arpfic/Organous_OSC/Hardware/carte_osc_fonctions_avancees_0.2_top.png

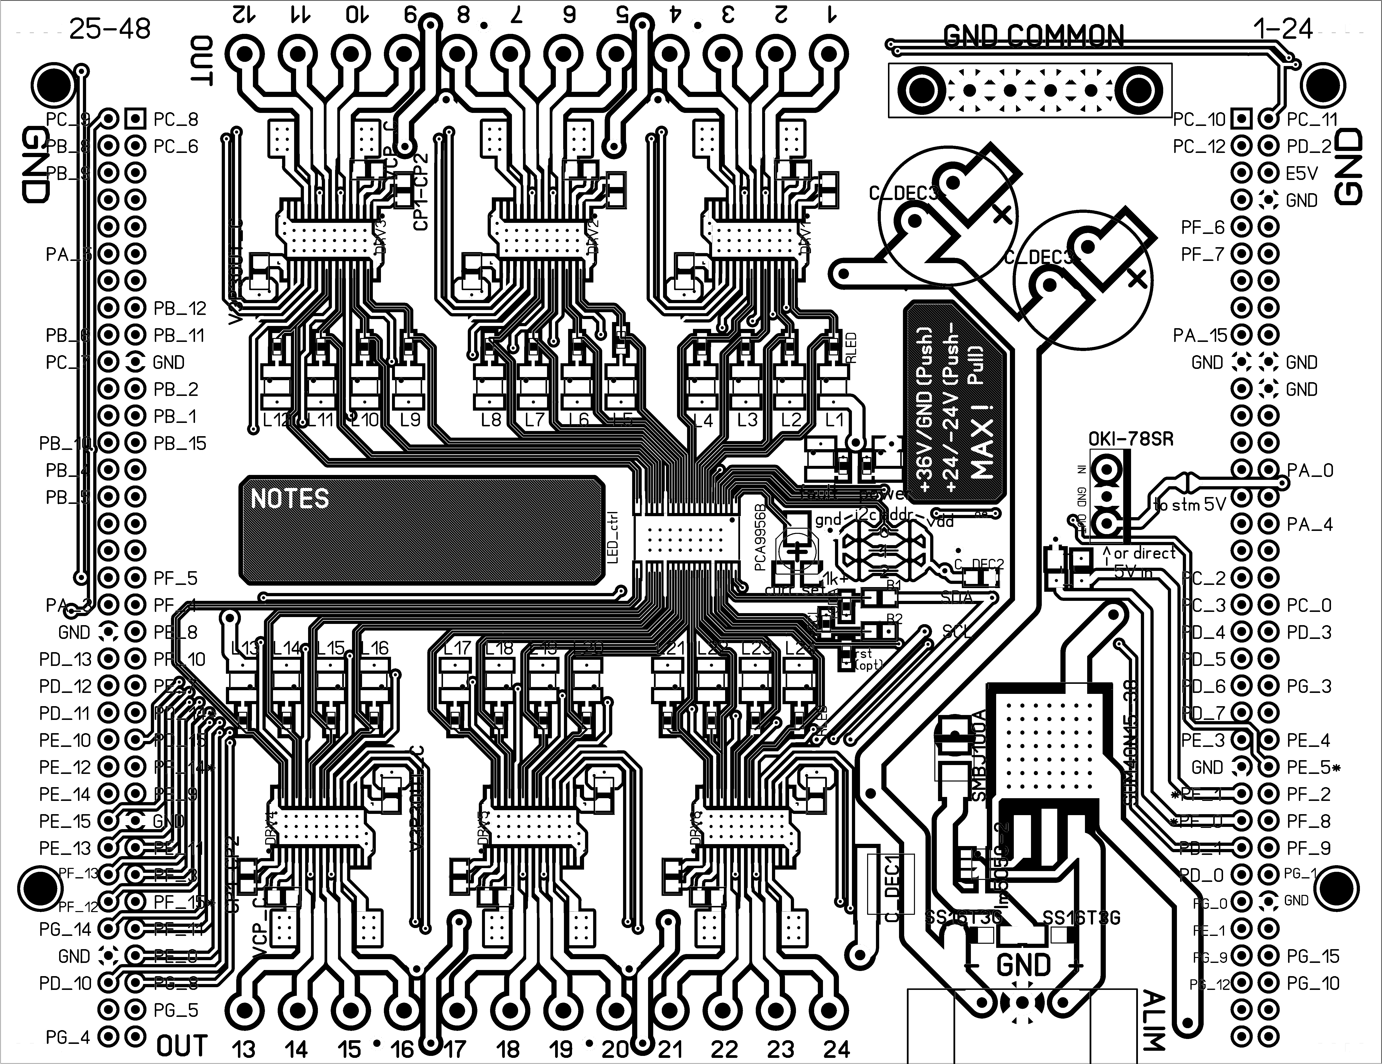
Hardware/carte_osc_fonctions_avancees_0.2_top.png
