arpfic/Organous_OSC/Hardware/carte_osc_schema_fonc.png

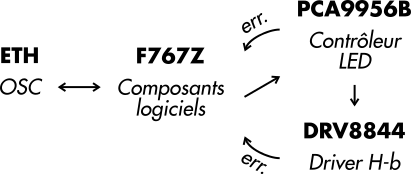
Hardware/carte_osc_schema_fonc.png
