arpfic/Organous_OSC/Hardware/Organous_OSC_v0.2_exemple.jpg

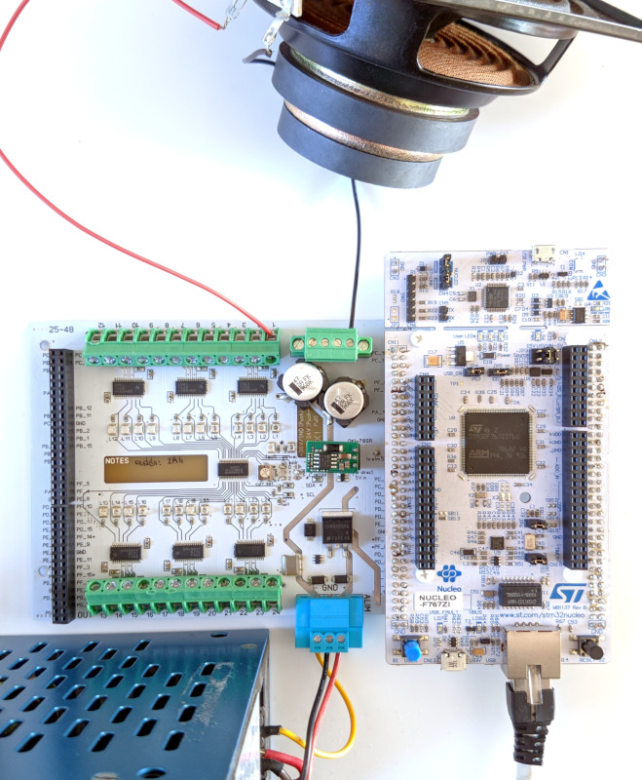
Hardware/Organous_OSC_v0.2_exemple.jpg
